OLIMEX/ESP32-GATEWAY/HARDWARE/Hardware revision H/3d/SOD123.step

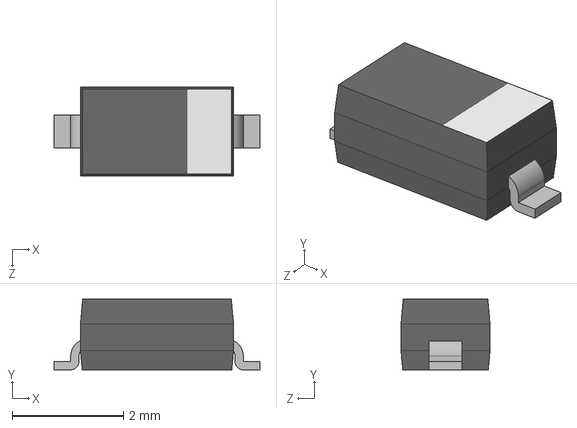
[picture p19: CAD file, 2019-12-09]
HARDWARE/Hardware revision H/3d/SOD123.step
3.70 x 1.27 x 1.60 mm
