OLIMEX/ESP32-GATEWAY/HARDWARE/Hardware revision H/3d/QFN32_5x5.step

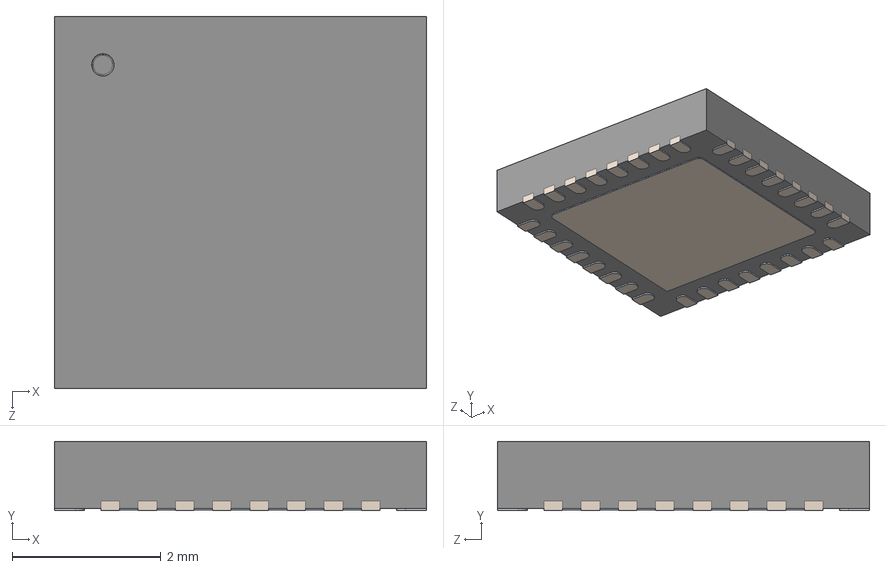
[picture p20: CAD file, 2019-12-09]
HARDWARE/Hardware revision H/3d/QFN32_5x5.step
5.00 x 0.93 x 5.00 mm
