OLIMEX/ESP32-GATEWAY/SOFTWARE/Newest-board-revisions/MOD-RTC/Pic1.jpg

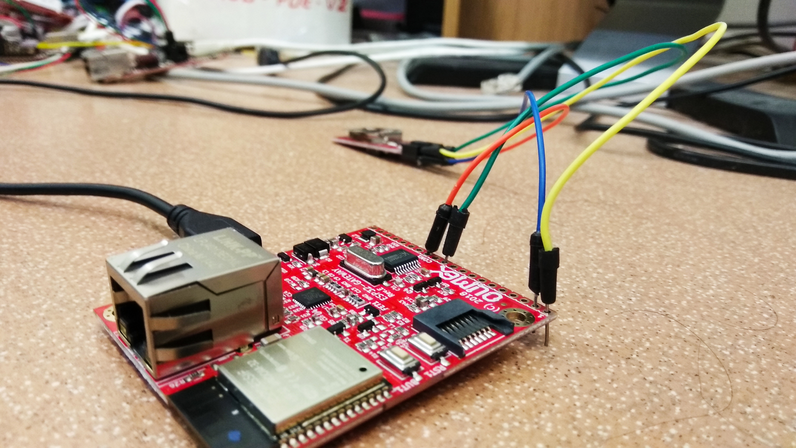
SOFTWARE/Newest-board-revisions/MOD-RTC/Pic1.jpg
