OLIMEX/ESP32-GATEWAY/SOFTWARE/Newest-board-revisions/MOD-RTC/Pic2.jpg

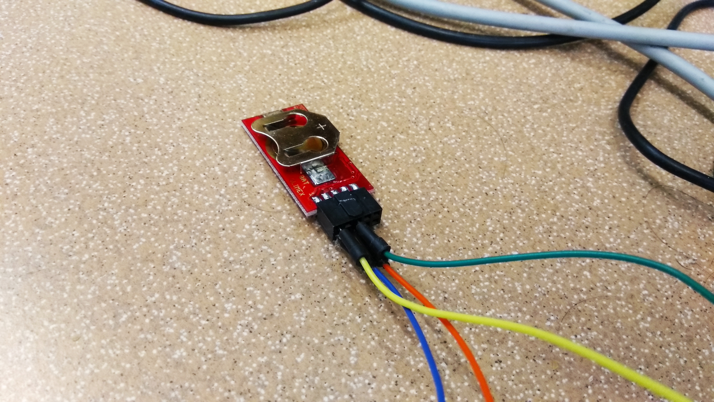
SOFTWARE/Newest-board-revisions/MOD-RTC/Pic2.jpg
